xyk2/nevco-mpc5-signal-decoder/oscilloscope_screenshots/TEK0005.BMP

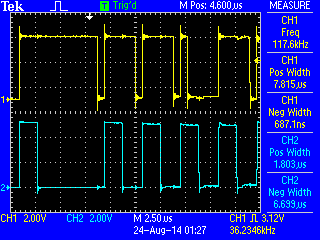
oscilloscope_screenshots/TEK0005.BMP
