xyk2/nevco-mpc5-signal-decoder/oscilloscope_screenshots/TEK0013.BMP

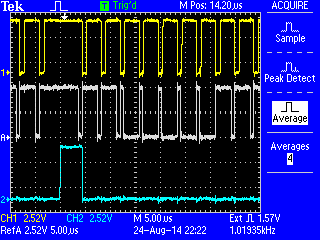
oscilloscope_screenshots/TEK0013.BMP
